automovil-uchile/V2017-1/Bibliografia/comportamiento.png

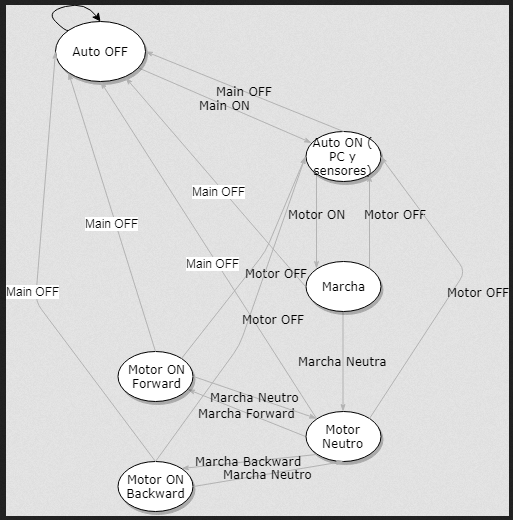
Bibliografia/comportamiento.png
